Bennett-Petzold/stenoswitch/pcb/resources/snap_magic/UJ20-C-H-G-SMT-P16-TR.step

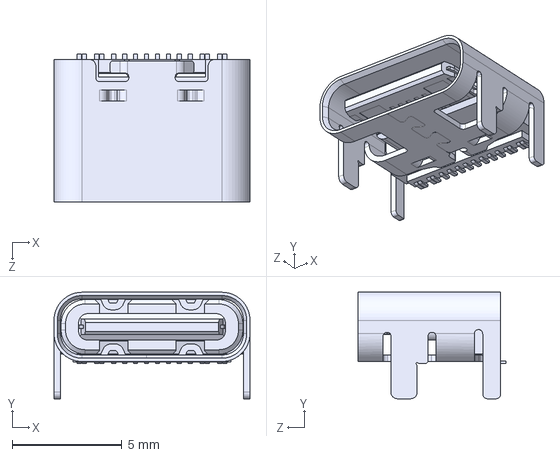
[picture p15: CAD file, 2025-08-30]
pcb/resources/snap_magic/UJ20-C-H-G-SMT-P16-TR.step
8.94 x 4.86 x 6.75 mm
