Bennett-Petzold/stenoswitch/pcb/resources/ultra_librarian/DPL0002A.stp

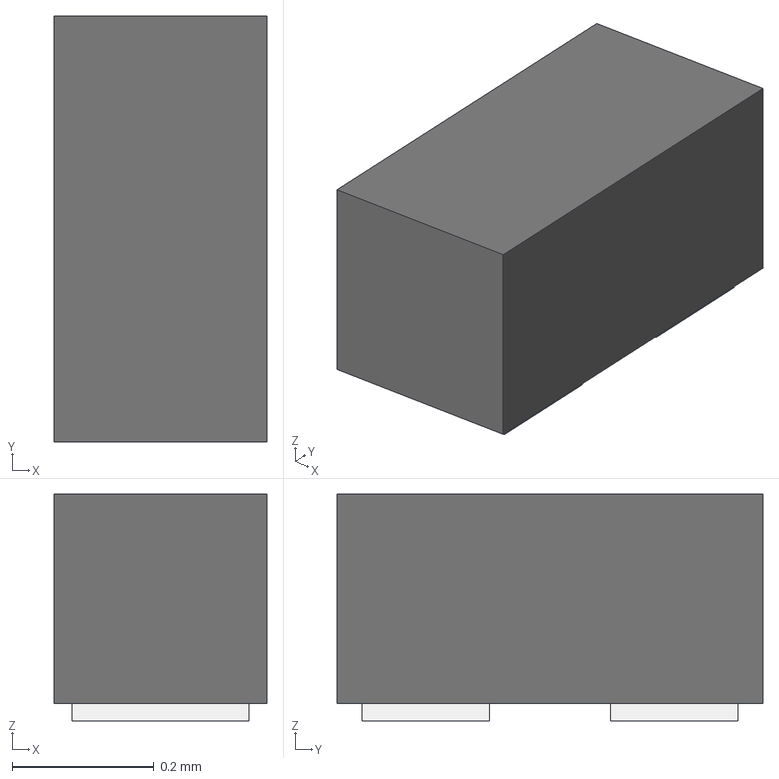
[picture p16: CAD file, 2025-08-30]
pcb/resources/ultra_librarian/DPL0002A.stp
0.3 x 0.6 x 0.32 mm
FRAME
MOLD
