Bennett-Petzold/stenoswitch/assembly/printed_aids/test_point_alignment/test_point_alignment.FCStd

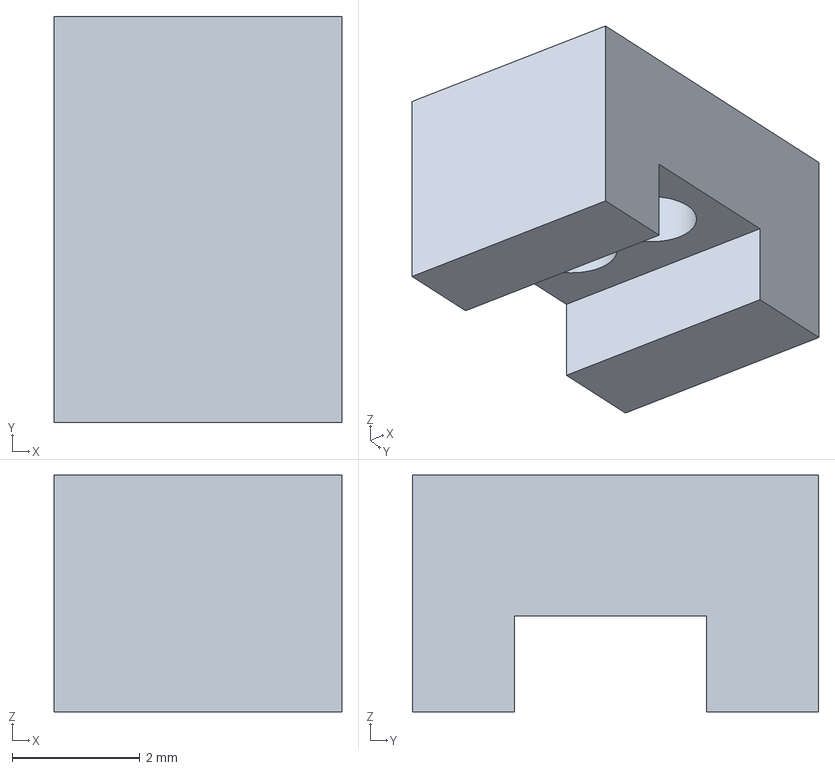
[picture p17: CAD file, 2026-01-25]
assembly/printed_aids/test_point_alignment/test_point_alignment.FCStd
4.50 x 6.35 x 3.70 mm
