Bennett-Petzold/stenoswitch/pcb/resources/snap_magic/0926-1-15-20-75-14-11-0.step

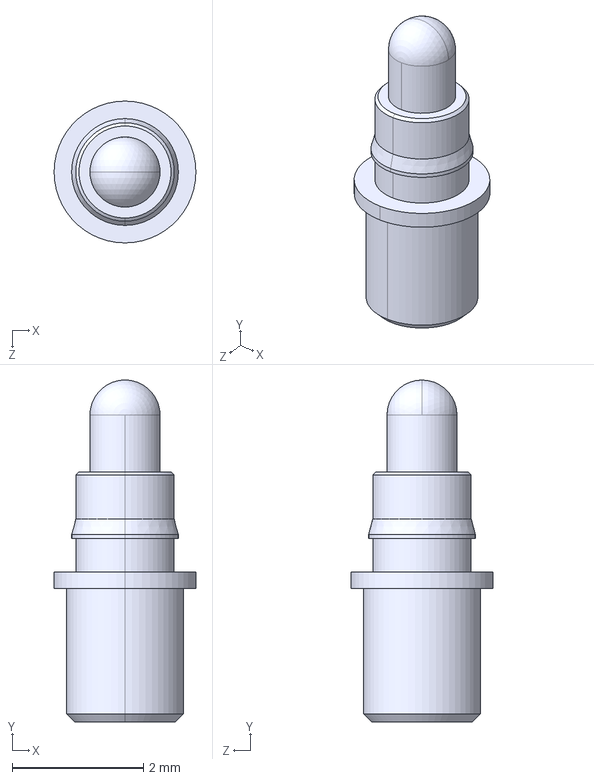
[picture p18: CAD file, 2025-08-30]
pcb/resources/snap_magic/0926-1-15-20-75-14-11-0.step
2.16 x 5.21 x 2.16 mm
