Bennett-Petzold/stenoswitch/pcb/resources/ultra_librarian/DYA0002A.stp

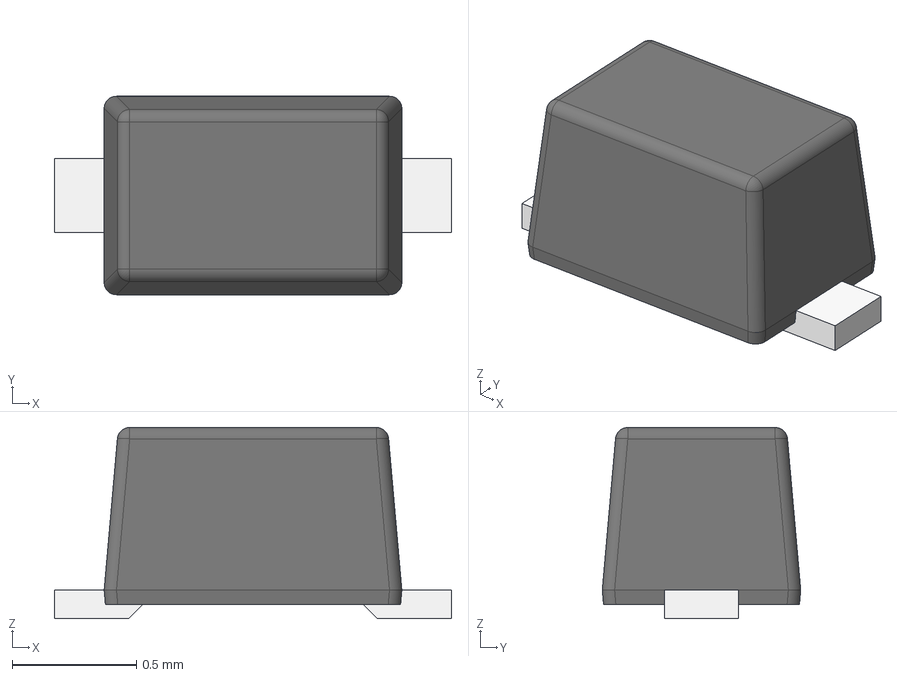
[picture p19: CAD file, 2025-08-30]
pcb/resources/ultra_librarian/DYA0002A.stp
1.60 x 0.8 x 0.77 mm
FRAME-DYA0002A
BODY-SOT
PIN1-ID
