Bennett-Petzold/stenoswitch/assembly/printed_aids/test_point_alignment/test_point_alignment_4.FCStd

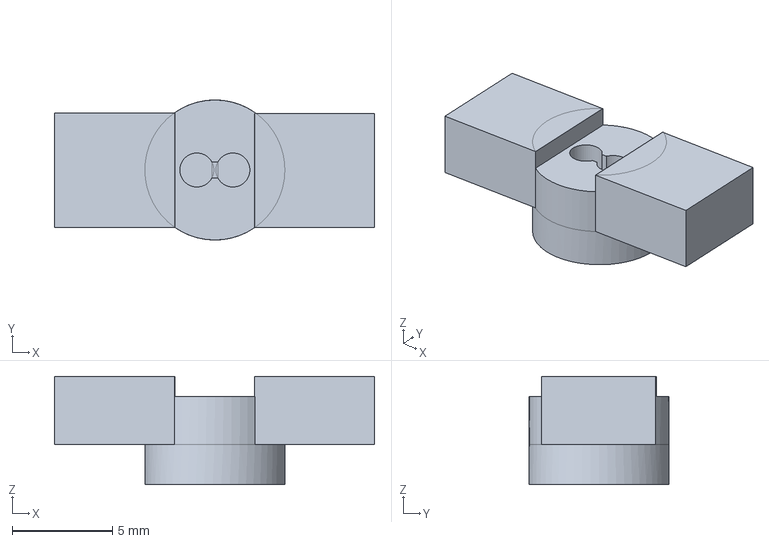
[picture p20: CAD file, 2026-01-25]
assembly/printed_aids/test_point_alignment/test_point_alignment_4.FCStd
16.0 x 7.00 x 5.40 mm
