Bennett-Petzold/stenoswitch/pcb/resources/manufacturer_provided/RA1H1CxxxR.stp

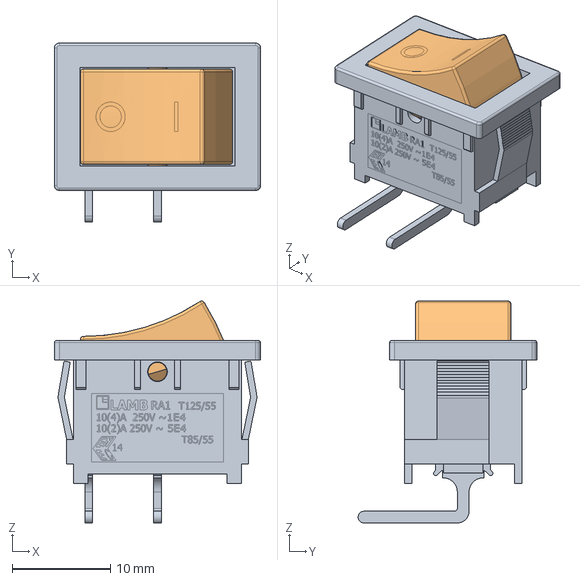
[picture p21: CAD file, 2025-08-10]
pcb/resources/manufacturer_provided/RA1H1CxxxR.stp
21.0 x 18.2 x 22.6 mm
