Bennett-Petzold/stenoswitch/pcb/resources/snap_magic/1043.step

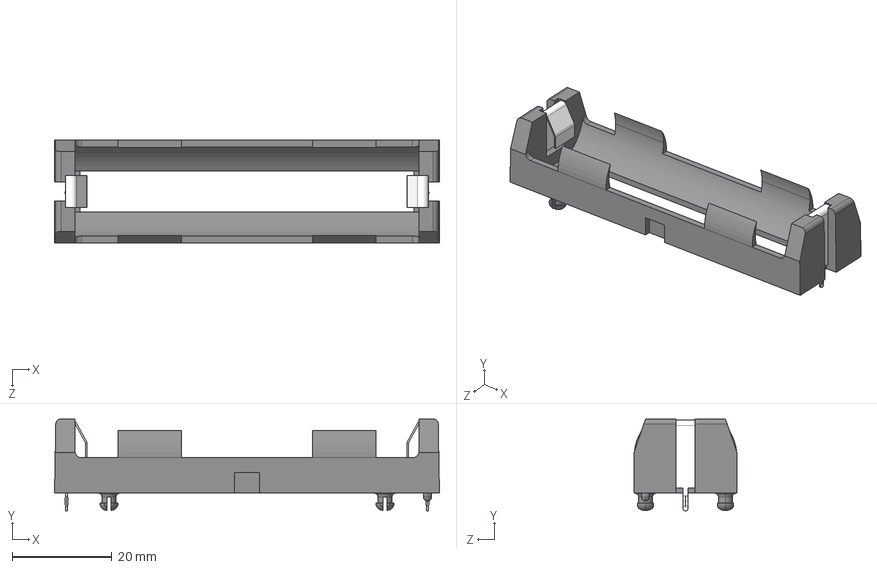
[picture p22: CAD file, 2025-08-09]
pcb/resources/snap_magic/1043.step
77.1 x 18.4 x 20.7 mm
