Bennett-Petzold/stenoswitch/pcb/resources/ultra_librarian/FUSE_ERBRE_PAN.step

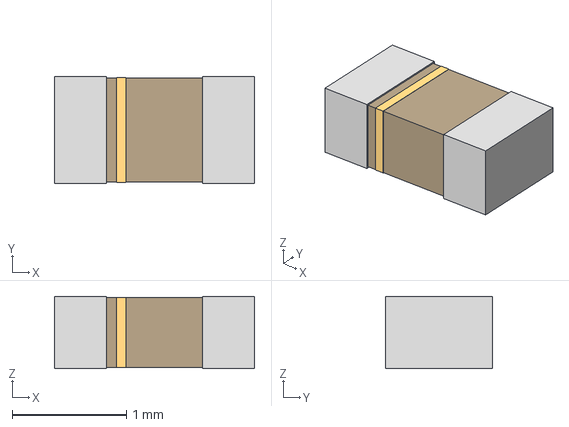
[picture p23: CAD file, 2025-08-25]
pcb/resources/ultra_librarian/FUSE_ERBRE_PAN.step
1.75 x 0.94 x 0.635 mm
