Bennett-Petzold/stenoswitch/assembly/printed_aids/test_point_alignment/test_point_alignment_5.FCStd

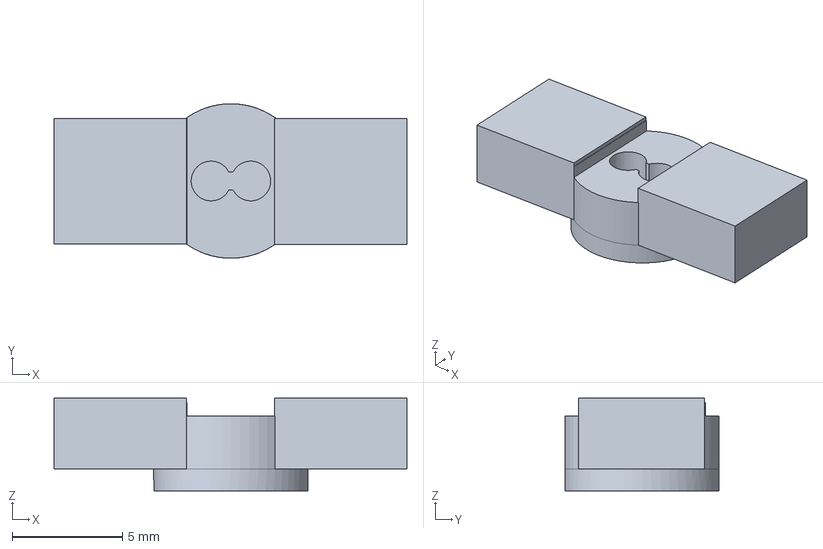
[picture p24: CAD file, 2026-01-25]
assembly/printed_aids/test_point_alignment/test_point_alignment_5.FCStd
16.0 x 7.00 x 4.20 mm
