Bennett-Petzold/stenoswitch/pcb/resources/manufacturer_provided/942.STEP

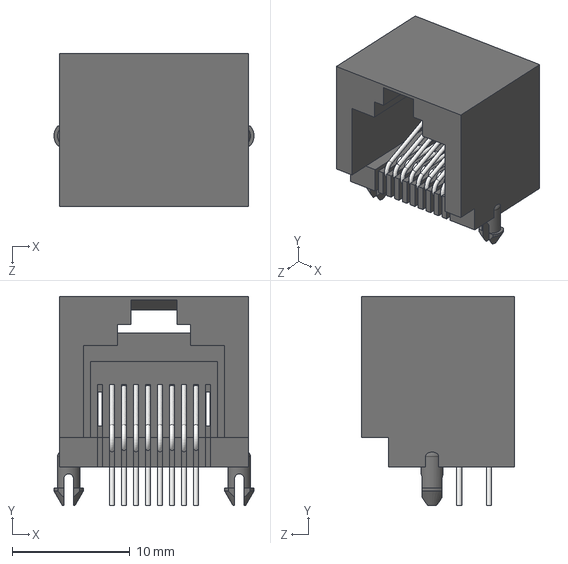
[picture p25: CAD file, 2025-08-09]
pcb/resources/manufacturer_provided/942.STEP
17.0 x 17.8 x 13.0 mm
