Bennett-Petzold/stenoswitch/pcb/resources/snap_magic/MCP40D19T-104E_LT.step

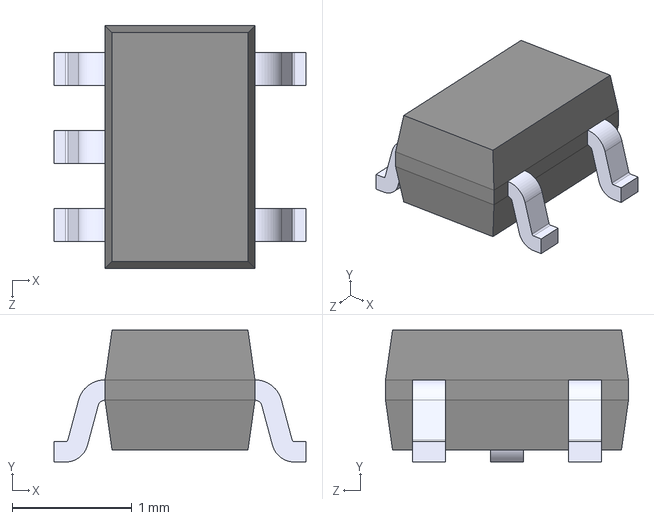
[picture p26: CAD file, 2025-08-08]
pcb/resources/snap_magic/MCP40D19T-104E_LT.step
2.10 x 1.10 x 2.02 mm
