Bennett-Petzold/stenoswitch/pcb/resources/ultra_librarian/DBZ0003A.stp

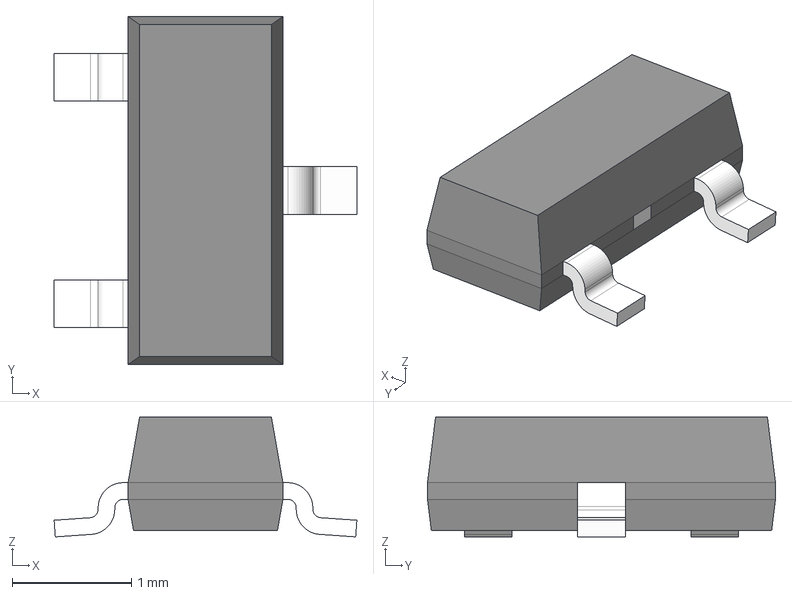
[picture p27: CAD file, 2025-08-10]
pcb/resources/ultra_librarian/DBZ0003A.stp
2.54 x 2.92 x 1.01 mm
BODY-SOT
LEAD-SOT x 3
PIN1-ID
TIEBAR
