Bennett-Petzold/stenoswitch/pcb/resources/ultra_librarian/SOIC14-N_MC_MCH.step

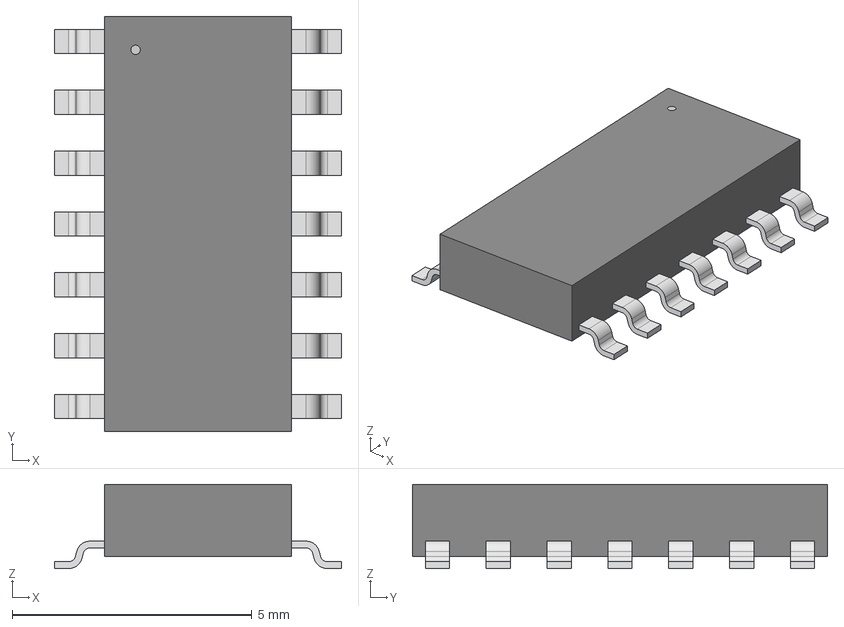
[picture p28: CAD file, 2025-08-10]
pcb/resources/ultra_librarian/SOIC14-N_MC_MCH.step
5.99 x 8.66 x 1.75 mm
