Bennett-Petzold/stenoswitch/pcb/resources/snap_magic/SLW-864587-2A-RA-N-D.step

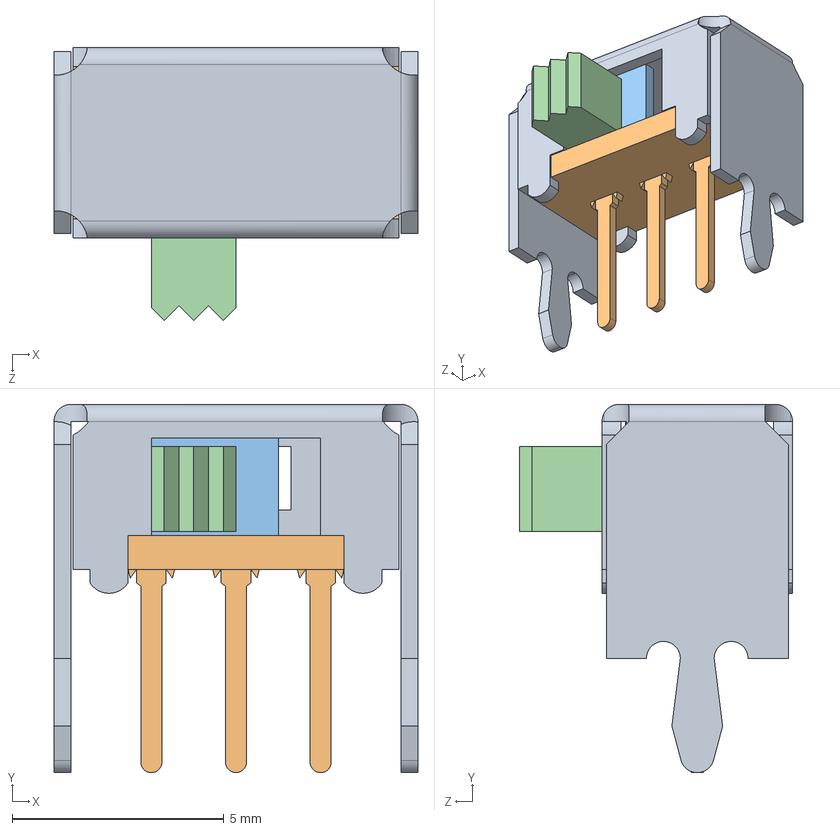
[picture p29: CAD file, 2025-08-04]
pcb/resources/snap_magic/SLW-864587-2A-RA-N-D.step
8.60 x 8.70 x 6.45 mm
