Bennett-Petzold/stenoswitch/pcb/resources/ultra_librarian/MP2637GR.step

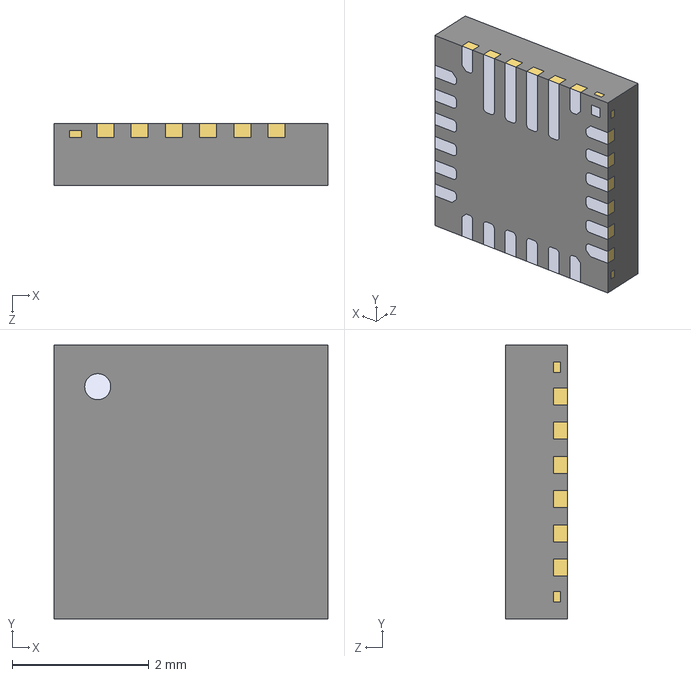
[picture p30: CAD file, 2025-08-10]
pcb/resources/ultra_librarian/MP2637GR.step
4.00 x 4.00 x 0.9 mm
