Bennett-Petzold/stenoswitch/pcb/resources/snap_magic/EG2208.step

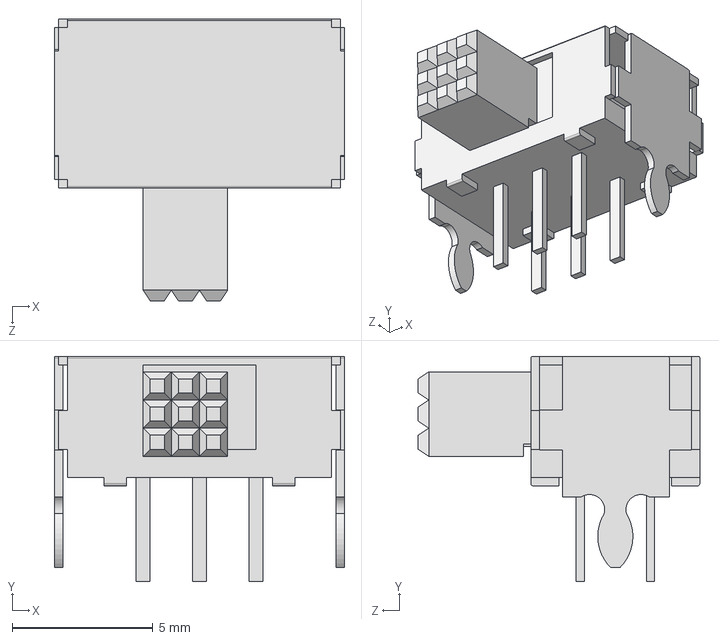
[picture p31: CAD file, 2025-08-04]
pcb/resources/snap_magic/EG2208.step
10.3 x 8.00 x 10.0 mm
