Bennett-Petzold/stenoswitch/pcb/resources/snap_magic/DMG2305UX-7.step

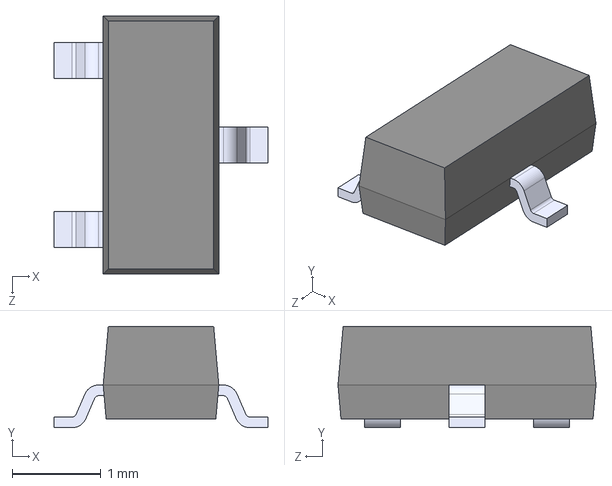
[picture p32: CAD file, 2025-08-04]
pcb/resources/snap_magic/DMG2305UX-7.step
2.40 x 1.14 x 2.90 mm
