Bennett-Petzold/stenoswitch/pcb/resources/snap_magic/USB4105-GF-A.step

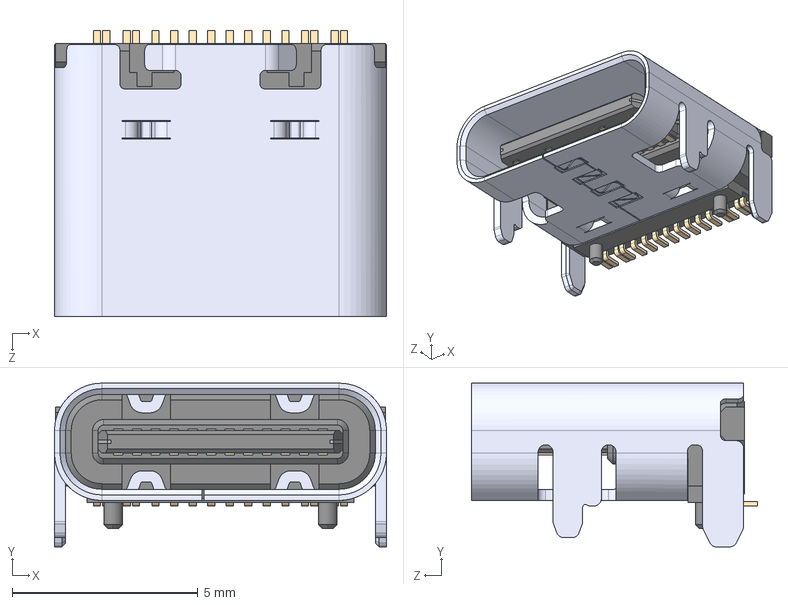
[picture p33: CAD file, 2025-08-04]
pcb/resources/snap_magic/USB4105-GF-A.step
8.94 x 4.41 x 7.71 mm
