Bennett-Petzold/stenoswitch/pcb/resources/snap_magic/1042.STEP

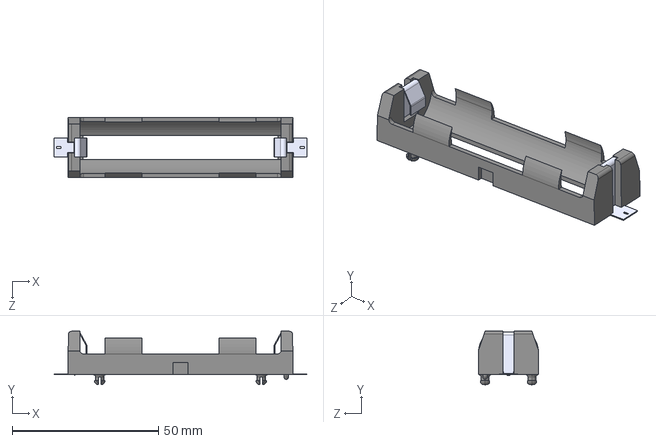
[picture p34: CAD file, 2025-08-04]
pcb/resources/snap_magic/1042.STEP
86.5 x 18.3 x 20.7 mm
