Bennett-Petzold/stenoswitch/software/rust/battery_control/src/chg_en.rs

use gpio_cdev::{Chip, LineHandle, LineRequestFlags};
use log::{debug, error, trace};

use crate::std_unwrap;

#[derive(Debug)]
pub struct ChgEn(LineHandle);

impl ChgEn {
    /// Defaults to disabled.
    pub fn new() -> Result<Self, gpio_cdev::Error> {
        trace!("Opening GPIO chip {:?}", option_env!("GPIO_CHIP"));
        let mut chip = Chip::new(option_env!("GPIO_CHIP").unwrap_or("/dev/null"))?;
        trace!("Opening GPIO line {:?}", option_env!("CHG_EN"));
        let this = Self(
            chip.get_line(std_unwrap(str::parse(
                option_env!("CHG_EN").unwrap_or("/dev/null"),
            )))?
            .request(LineRequestFlags::OUTPUT, 0, "battery_control")?,
        );
        this.disable()?;
        Ok(this)
    }
}

impl ChgEn {
    pub fn enable(&self) -> Result<(), gpio_cdev::Error> {
        trace!("Enabling charging");
        self.0.set_value(1)
    }

    pub fn disable(&self) -> Result<(), gpio_cdev::Error> {
        trace!("Disabling charging");
        self.0.set_value(0)
    }

    pub fn is_enabled(&self) -> Result<bool, gpio_cdev::Error> {
        self.0.get_value().map(|x| x == 1)
    }
}

impl Drop for ChgEn {
    fn drop(&mut self) {
        // Attempt to disable on drop
        if let Err(e) = self.disable() {
            error!("Failure to disable ChgEn on drop: {e:#?}");
        };
    }
}
