Bennett-Petzold/stenoswitch/software/rust/keyboard/src/scan.rs

use std::{
    io,
    ops::{Deref, DerefMut},
    simd::{self, Simd, num::SimdUint, simd_swizzle},
    sync::{Arc, Condvar, Mutex, MutexGuard, mpsc},
    thread,
    time::{Duration, Instant, SystemTime},
};

use gpio_cdev::{Chip, EventRequestFlags, LineEventHandle, LineHandle, LineRequestFlags};
use log::{debug, trace, warn};
use nix::{
    sys::time::TimeValLike,
    time::{ClockId, clock_gettime},
};

const GEMINI_PR_BYTES: usize = 6;

/// GeminiPR Steno packet.
///
/// Reference is <https://docs.qmk.fm/features/stenography#geminipr>.
///
/// ```ignore
/// 1 Fn  #1  #2 #3 #4 #5   #6
/// 0 S1- S2- T- K- P- W-   H-
/// 0 R-  A-  O- *1 *2 res1 res2
/// 0 pwr *3  *4 -E -U -F   -R
/// 0 -P  -B  -L -G -T -S   -D
/// 0 #7  #8  #9 #A #B #C   -Z
/// ```
#[derive(Debug)]
pub struct GeminiPr([u8; GEMINI_PR_BYTES]);

impl GeminiPr {
    /// Creates a new empty packet.
    pub const fn new() -> Self {
        let mut inner = [0; GEMINI_PR_BYTES];
        inner[0] = 0b1;
        Self(inner)
    }
}

impl Default for GeminiPr {
    fn default() -> Self {
        Self::new()
    }
}

impl Deref for GeminiPr {
    type Target = [u8; 6];
    fn deref(&self) -> &Self::Target {
        &self.0
    }
}

impl DerefMut for GeminiPr {
    fn deref_mut(&mut self) -> &mut Self::Target {
        &mut self.0
    }
}

/// Size of a full keyboard scan.
///
/// 3 rows
/// (5 * 2) columns
const RAW_SCAN_LEN: usize = 30;

/// [`RAW_SCAN_LEN`] with SIMD pad, two blank.
const RAW_SCAN_LEN_SIMD: usize = 32;

/// First 30 elements are scan results.
///
/// Last elements are guaranteed to be 0 (false).
#[derive(Debug, Clone, Copy, PartialEq, Eq, PartialOrd, Ord, Hash)]
struct RawScan(Simd<u8, RAW_SCAN_LEN_SIMD>);

impl RawScan {
    #[inline]
    pub const fn new() -> Self {
        let scan_values = Simd::splat(0);
        Self(scan_values)
    }

    #[inline]
    /// Fills from array with the expected scan order.
    ///
    /// Rows 0-2, columns right 0-4 then left 0-4 for each row.
    pub fn from_scan(scan: [u8; RAW_SCAN_LEN]) -> Self {
        let mut this = Self::new();
        this.0[..RAW_SCAN_LEN].copy_from_slice(&scan);
        this
    }

    #[inline]
    /// Add new values to the total scan.
    pub fn extend(&mut self, new: Self) {
        self.0 |= new.0;
    }

    #[inline]
    /// The number of scanned keys.
    pub fn len(&self) -> u8 {
        // All keys are 0 (not scanned) or 1 (scanned).
        self.0.reduce_sum()
    }

    #[inline]
    /// Returns true when no keys were scanned.
    pub fn is_empty(&self) -> bool {
        // All keys are 0 (not scanned) or 1 (scanned).
        self.0.reduce_or() == 0
    }

    #[inline]
    pub fn update_gemini(mut self, packet: &mut GeminiPr) {
        // Rows go 0 to 2 in order.
        // Columns are right 0 to 4, then left 0 to 4.
        // Produces this, concated in order:
        //
        // Row 0
        // [-T, -L, -P, -F, *3]
        // [S1-, T-, P-, H-, *1]
        //
        // Row 1
        // [-S, -G, -B, -R, *4]
        // [S2-, K-, W-, R-, *2]
        //
        // Row 2
        // [-Z, -D, #C, -U, -E]
        // [res2, res1, #B, A-, O-]
        //
        // Trailing:
        // [always 0, always 0]
        //
        // Output after reloc is
        // [S1-, S2-, T-, K-, P-, W-, H-]
        // [R-, A-, O-, *1, *2, res1, res2]
        // [_(always 0), *3, *4, -E, -U, -F, -R]
        // [-P, -B, -L, -G, -T, -S, -D]
        // [#B, #C, -Z]
        const RELOCS: [usize; RAW_SCAN_LEN_SIMD] = [
            5, 15, 0, 16, 2, 17, 8, // [S1-, S2-, T-, K-, P-, W-, H-]
            0, 0, 0, 0, 0, 0, 0, // [R-, A-, O-, *1, *2, res1, res2]
            31, 0, 0, 0, 0, 0, 0, // [_(always 0), *3, *4, -E, -U, -F, -R]
            0, 0, 0, 0, 0, 0, 0, // [-P, -B, -L, -G, -T, -S, -D]
            0, 0, 31, 31, // [#B, #C, -Z, _(always 0), _(always 0)]
        ];

        // MSB order with 4 chunks of 7, one chunk of 3, one trailing
        const SHIFTS: Simd<u8, RAW_SCAN_LEN_SIMD> = Simd::from_array([
            6, 5, 4, 3, 2, 1, 0, 6, 5, 4, 3, 2, 1, 0, 6, 5, 4, 3, 2, 1, 0, 6, 5, 4, 3, 2, 1, 0, 2,
            1, 0, 0,
        ]);

        // Change positions for GeminiPR splits
        // Organized in lines of 7 bits
        self.0 = simd_swizzle!(self.0, RELOCS);
        self.0 <<= SHIFTS;

        // Shrink into individual chunks
        let row1 = self.0.extract::<{ 7 * 0 }, 7>();
        let row2 = self.0.extract::<{ 7 * 1 }, 7>();
        let row3 = self.0.extract::<{ 7 * 2 }, 7>();
        let row4 = self.0.extract::<{ 7 * 3 }, 7>();
        let row5 = self.0.extract::<{ 7 * 4 }, 4>();
        let simd_split = [row1, row2, row3, row4];

        debug!(
            "GeminiPR split rows: {:#?}",
            [
                row1.as_array().as_slice(),
                row2.as_array().as_slice(),
                row3.as_array().as_slice(),
                row4.as_array().as_slice(),
                row5.as_array().as_slice()
            ]
        );

        // Convert to single bytes and write in.
        // First row is left as default, the keyboard never changes those
        // values.
        for (packet, new) in packet.iter_mut().skip(1).zip(simd_split) {
            *packet = new.reduce_or();
        }

        // Final row is shorter than the rest.
        packet[5] = row5.reduce_or();
    }

    #[inline]
    pub fn create_gemini(self) -> GeminiPr {
        let mut packet = GeminiPr::new();
        self.update_gemini(&mut packet);
        packet
    }
}

impl Default for RawScan {
    fn default() -> Self {
        Self::new()
    }
}

#[derive(Debug)]
pub enum MaybeLine<'a> {
    Locked(&'a Mutex<LineEventHandle>),
    Unlocked(MutexGuard<'a, LineEventHandle>),
}

impl<'a> From<&'a Mutex<LineEventHandle>> for MaybeLine<'a> {
    fn from(value: &'a Mutex<LineEventHandle>) -> Self {
        Self::Locked(value)
    }
}

impl MaybeLine<'_> {
    /// Returns the actual value if the guard is available.
    ///
    /// Returns 0 if the mutex is being held (no rising event triggered means
    /// the key must be unpressed).
    ///
    /// There is a timing penalty whenever a mutex is newly claimed. Failing
    /// the mutex lock should have a consistent atomic penalty. Once a handle
    /// is held, that will have a consistent timing (no atomic check necessary).
    fn get_value(&mut self) -> Result<u8, gpio_cdev::Error> {
        match self {
            Self::Locked(handle) => {
                if let Ok(guard) = handle.try_lock() {
                    *self = Self::Unlocked(guard);
                    self.get_value()
                } else {
                    Ok(0)
                }
            }
            Self::Unlocked(guard) => guard.get_value(),
        }
    }
}

#[derive(Debug)]
pub struct KeyScanner {
    rows: [LineHandle; 3],
    // Right hand columns first
    columns: [Arc<Mutex<LineEventHandle>>; 10],
    // Captures the event times of all rising edges
    line_events: mpsc::Receiver<u64>,
}

impl KeyScanner {
    pub fn new() -> Result<Self, gpio_cdev::Error> {
        const ROW_ENV: [&str; 3] = ["ROW0", "ROW1", "ROW2"];
        const RHS_COLUMNS: [&str; 5] = ["RCOL0", "RCOL1", "RCOL2", "RCOL3", "RCOL4"];
        const LHS_COLUMNS: [&str; 5] = ["LCOL0", "LCOL1", "LCOL2", "LCOL3", "LCOL4"];

        let mut chip = Chip::new(option_env!("GPIO_CHIP").unwrap_or("/dev/null"))?;

        let rows = [
            chip.get_line(str::parse(option_env!("ROW0").unwrap_or("/dev/null")).unwrap())?
                .request(LineRequestFlags::OUTPUT, 0, "keyboard_scan")?,
            chip.get_line(str::parse(option_env!("ROW1").unwrap_or("/dev/null")).unwrap())?
                .request(LineRequestFlags::OUTPUT, 0, "keyboard_scan")?,
            chip.get_line(str::parse(option_env!("ROW2").unwrap_or("/dev/null")).unwrap())?
                .request(LineRequestFlags::OUTPUT, 0, "keyboard_scan")?,
        ];

        let raw_columns = [
            chip.get_line(str::parse(option_env!("RCOL0").unwrap_or("/dev/null")).unwrap())?,
            chip.get_line(str::parse(option_env!("RCOL1").unwrap_or("/dev/null")).unwrap())?,
            // PROBLEM LINE
            chip.get_line(str::parse(option_env!("RCOL2").unwrap_or("/dev/null")).unwrap())?,
            //
            // PROBLEM LINE
            chip.get_line(str::parse(option_env!("RCOL3").unwrap_or("/dev/null")).unwrap())?,
            //
            chip.get_line(str::parse(option_env!("RCOL4").unwrap_or("/dev/null")).unwrap())?,
            // PROBLEM LINE
            chip.get_line(str::parse(option_env!("LCOL0").unwrap_or("/dev/null")).unwrap())?,
            //
            chip.get_line(str::parse(option_env!("LCOL1").unwrap_or("/dev/null")).unwrap())?,
            chip.get_line(str::parse(option_env!("LCOL2").unwrap_or("/dev/null")).unwrap())?,
            chip.get_line(str::parse(option_env!("LCOL3").unwrap_or("/dev/null")).unwrap())?,
            chip.get_line(str::parse(option_env!("LCOL4").unwrap_or("/dev/null")).unwrap())?,
        ];

        let columns = raw_columns.map(|col| {
            Arc::new(Mutex::new(
                col.events(
                    LineRequestFlags::INPUT | LineRequestFlags::BIAS_PULL_DOWN,
                    EventRequestFlags::RISING_EDGE,
                    "keyboard_scan",
                )
                .unwrap(),
            ))
        });

        // Only accept one event at a time and block all event threads when no
        // events are occuring.
        let (line_events_tx, line_events) = mpsc::sync_channel(0);

        // Wait for any key to be pressed.
        // Since the events are blocking, each column needs its own thread.
        // These will be cleaned up on struct drop due to receiver drop.
        for column in &columns {
            let tx = line_events_tx.clone();
            let column = column.clone();
            let _monitor_column_thread = thread::spawn(move || {
                loop {
                    // Only hold the mutex while waiting on an event.
                    // Otherwise the mutex would be held over `send`.
                    // If other threads can't claim the mutex, the column is
                    // presumed to be off.
                    let maybe_event = { column.lock().unwrap().get_event() };

                    if let Ok(event) = maybe_event {
                        // Events will block here while the keyboard is being
                        // actively scanned for a new packet.
                        tx.send(event.timestamp()).unwrap();
                    }
                }
            });
        }

        Ok(Self {
            rows,
            columns,
            line_events,
        })
    }

    /// Blocks until a key is pressed.
    pub fn wait_for_input(&mut self) -> Result<(), gpio_cdev::Error> {
        let start_time = clock_gettime(ClockId::CLOCK_MONOTONIC)
            .expect("Well defined Linux call")
            .num_nanoseconds()
            .try_into()
            .unwrap_or(0_u64);

        // Turning on all rows means any key will trigger a press
        for row in &self.rows {
            row.set_value(1)?;
        }

        debug!("Waiting for input");
        loop {
            let event = self.line_events.recv().unwrap();
            // Discard all prior events.
            // A previous keyboard scan will produce a lot of these.
            if event >= start_time {
                trace!("Accepted event: {event} >= {start_time}");
                return Ok(());
            } else {
                trace!("Rejected past event: {event} < {start_time}");
            }
        }
    }

    pub fn verify_scan(&self) {
        for row in &self.rows {
            row.set_value(1).unwrap();
        }

        let mut columns = self
            .columns
            .each_ref()
            .map(|col| MaybeLine::from(col.as_ref()));

        let mut existing_detect = false;
        loop {
            let detect = columns
                .iter_mut()
                .map(|col| col.get_value().unwrap())
                .any(|val| val == 1);

            if detect != existing_detect {
                existing_detect = detect;
                if detect {
                    let values = columns.each_mut().map(|col| col.get_value().unwrap());
                    warn!("KEY PRESS: {:?}, {:#?}", values, SystemTime::now());
                }
            }
        }
    }

    /// Scans at an effective 133 KHz.
    pub fn scan(&self) -> Result<GeminiPr, gpio_cdev::Error> {
        /// Assuming the lines can handle 400 KHz.
        const LINE_DELAY: Duration = Duration::from_nanos(2500);
        /// Number of consecutive zero scans to end packet collection.
        const EMPTY_TO_END: u8 = 10;

        let mut empty_count = 0;
        let mut data = RawScan::new();

        for row in &self.rows {
            row.set_value(0)?;
        }
        // Turn the first line off and give the levels time to fall.
        spin_sleep::sleep(LINE_DELAY);

        let mut columns = self
            .columns
            .each_ref()
            .map(|col| MaybeLine::from(col.as_ref()));
        debug!("Starting keyboard scan...");

        while empty_count < EMPTY_TO_END {
            let mut new_data = [0; 30];
            for (row_num, row) in self.rows.iter().enumerate() {
                row.set_value(1)?;
                spin_sleep::sleep(LINE_DELAY);

                let base_idx = row_num * 10;
                for (dest, column) in new_data[base_idx..(base_idx + 10)]
                    .iter_mut()
                    .zip(&mut columns)
                {
                    *dest = column.get_value()?;
                }
                row.set_value(0)?;
            }

            let new_data = RawScan::from_scan(new_data);

            // Branchless tomfoolery to update the empty count
            {
                // Bool definition gives 0 for false, 1 for true.
                let empty = new_data.is_empty() as u8;
                // Increases the count when empty
                empty_count += empty;
                // Resets to zero when nonempty
                empty_count *= empty;
            }

            data.extend(new_data);
        }

        debug!("Finished keyboard scan, raw scan: {data:?}");

        Ok(data.create_gemini())
    }
}
